mylestunglee/articulation70/images/kicad_left.png

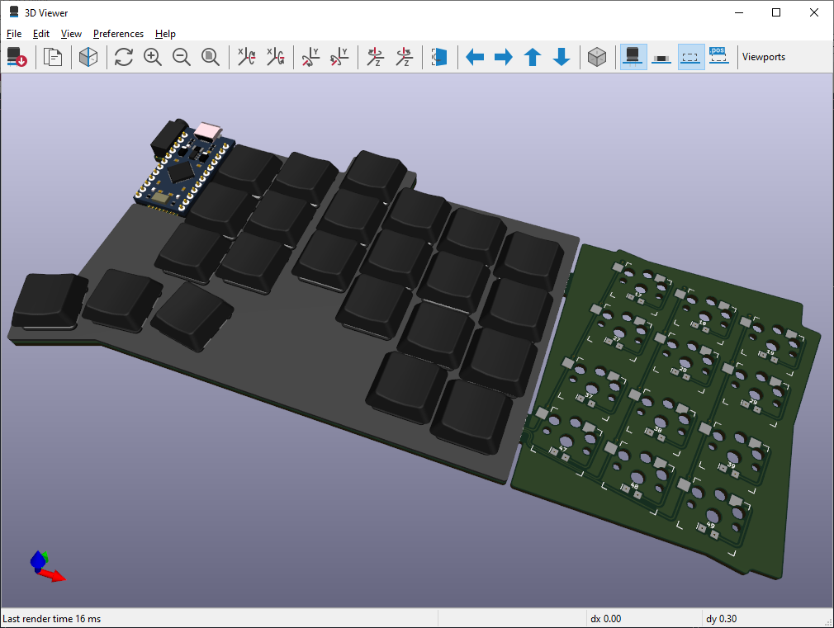
images/kicad_left.png
