mylestunglee/articulation70/images/kicad_plugin1_frames/04.png

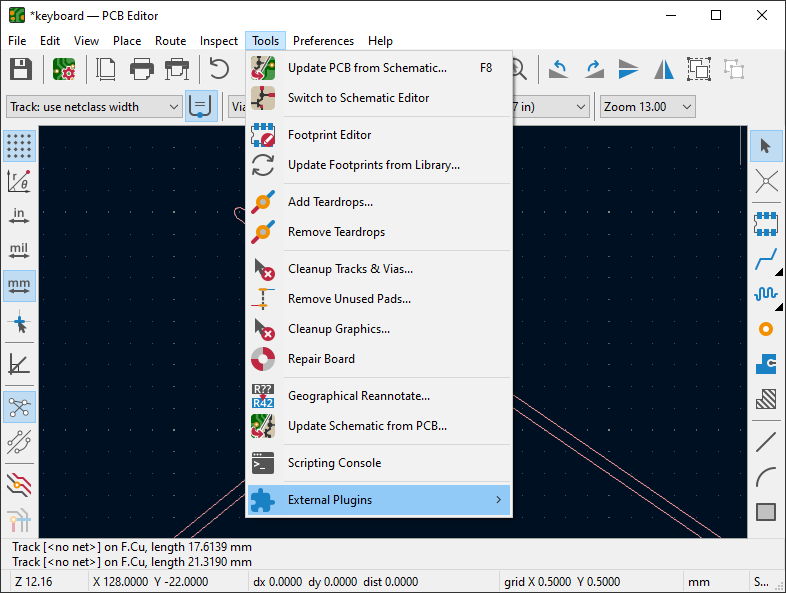
images/kicad_plugin1_frames/04.png
