mylestunglee/articulation70/images/kicad_plugin1_frames/07.png

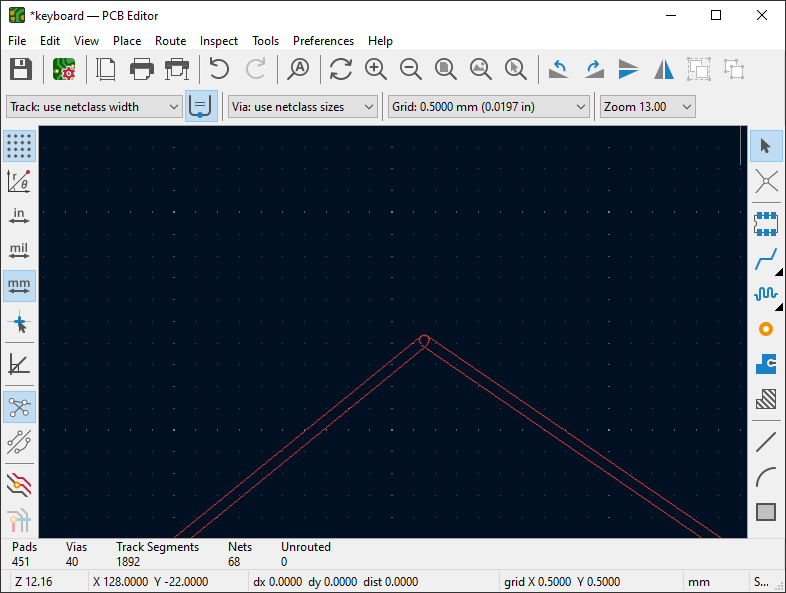
images/kicad_plugin1_frames/07.png
