mylestunglee/articulation70/images/kicad_plugin1_frames/09.png

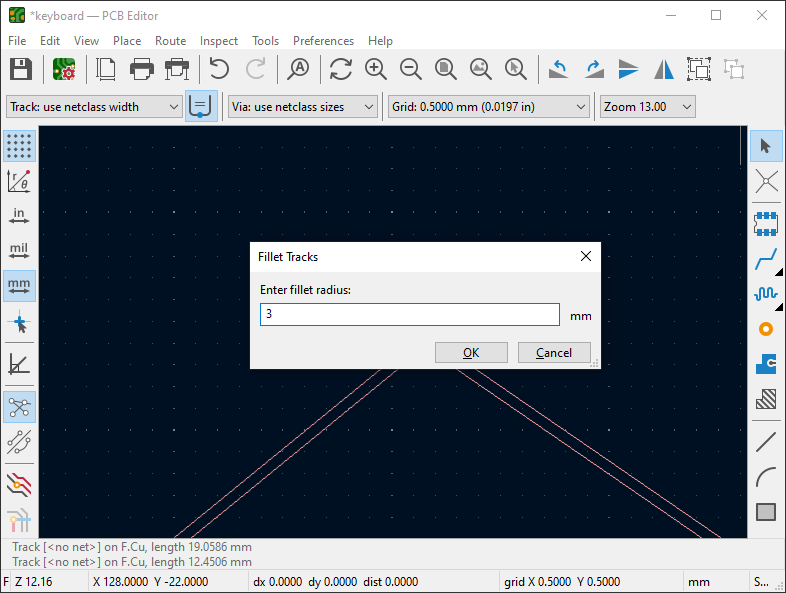
images/kicad_plugin1_frames/09.png
