mylestunglee/articulation70/images/photos/image1.jpeg

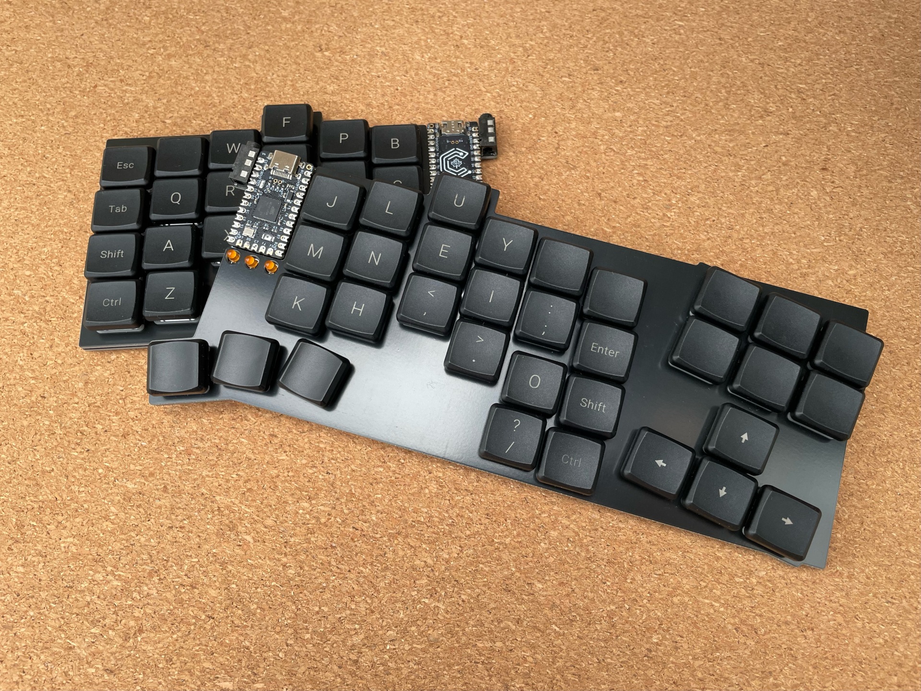
images/photos/image1.jpeg
