mylestunglee/articulation70/images/photos/image2.jpeg

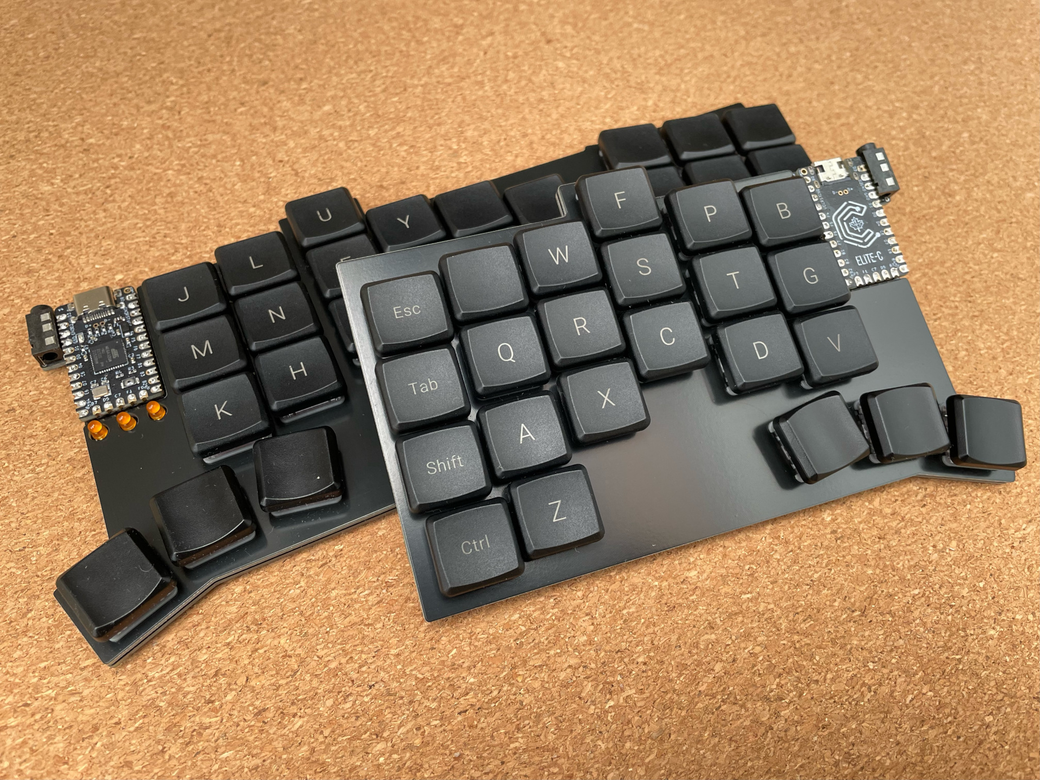
images/photos/image2.jpeg
