mylestunglee/articulation70/images/photos/image3.jpeg

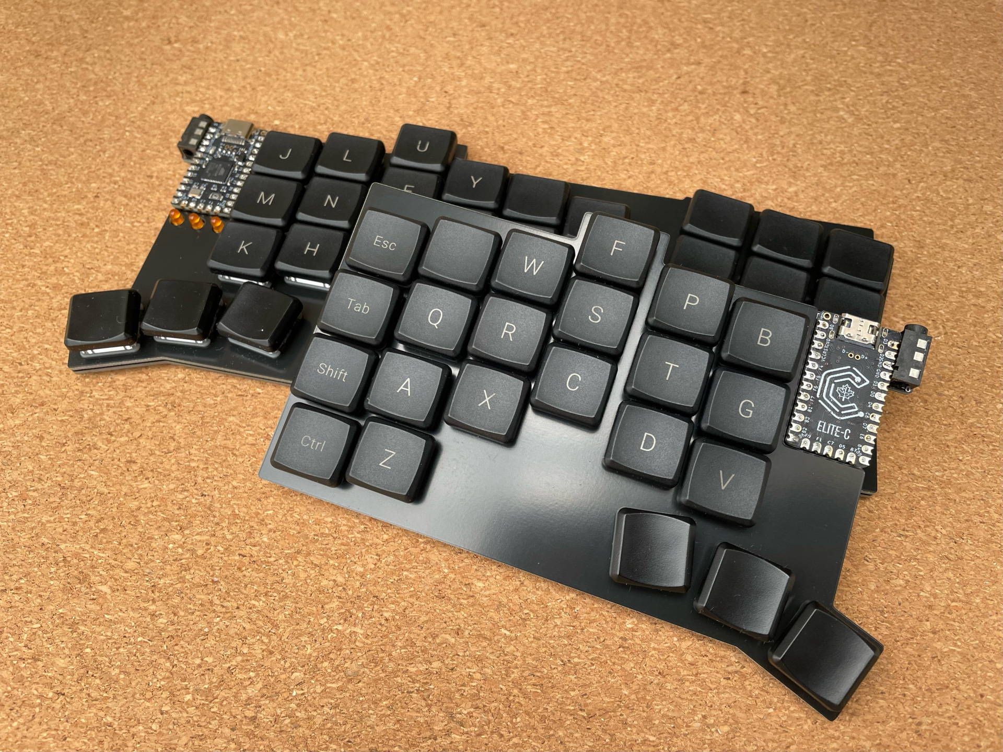
images/photos/image3.jpeg
