mylestunglee/articulation70/images/photos/image4.jpeg

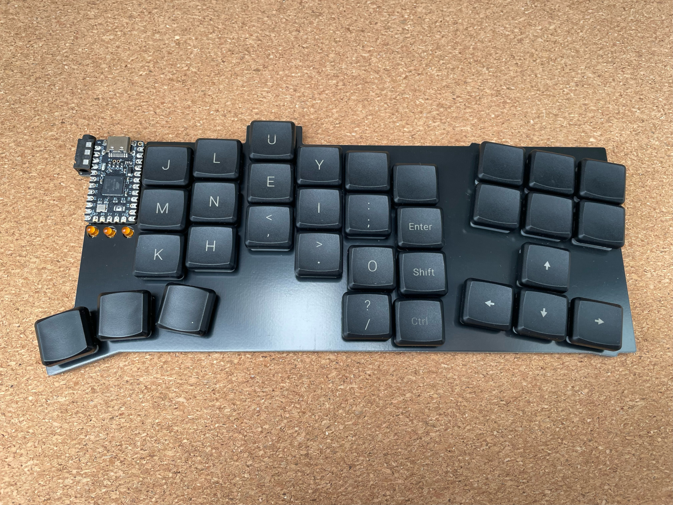
images/photos/image4.jpeg
