mylestunglee/articulation70/images/photos/image5.jpeg

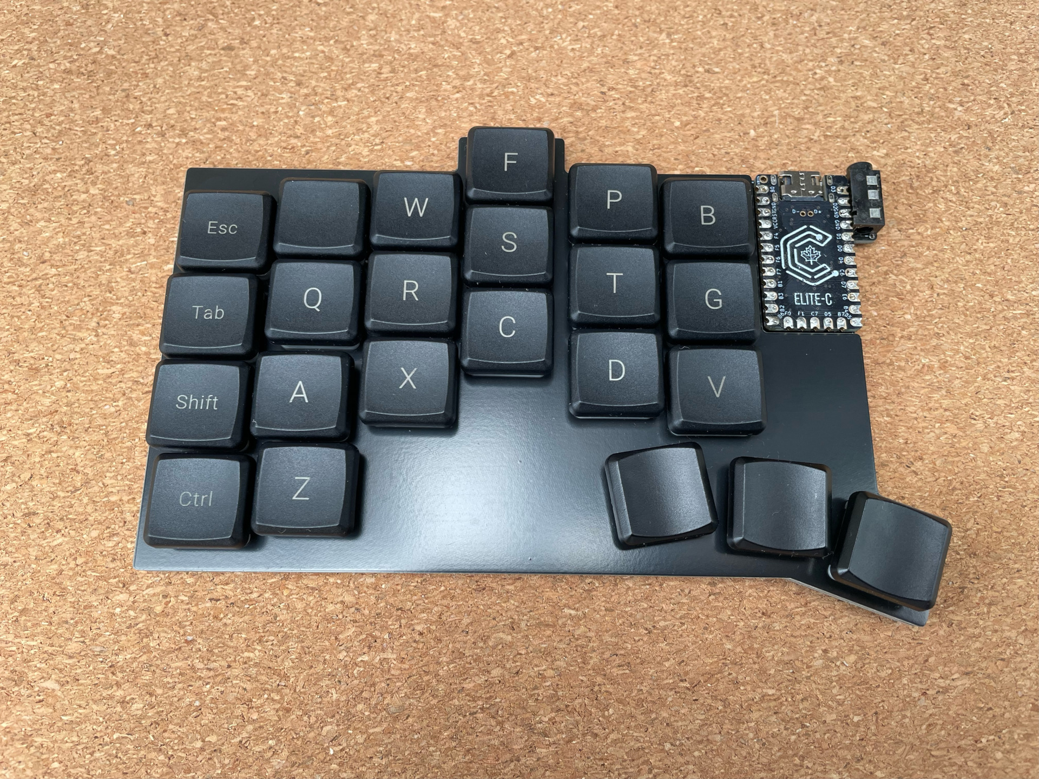
images/photos/image5.jpeg
