mylestunglee/articulation70/images/photos/pcb.jpeg

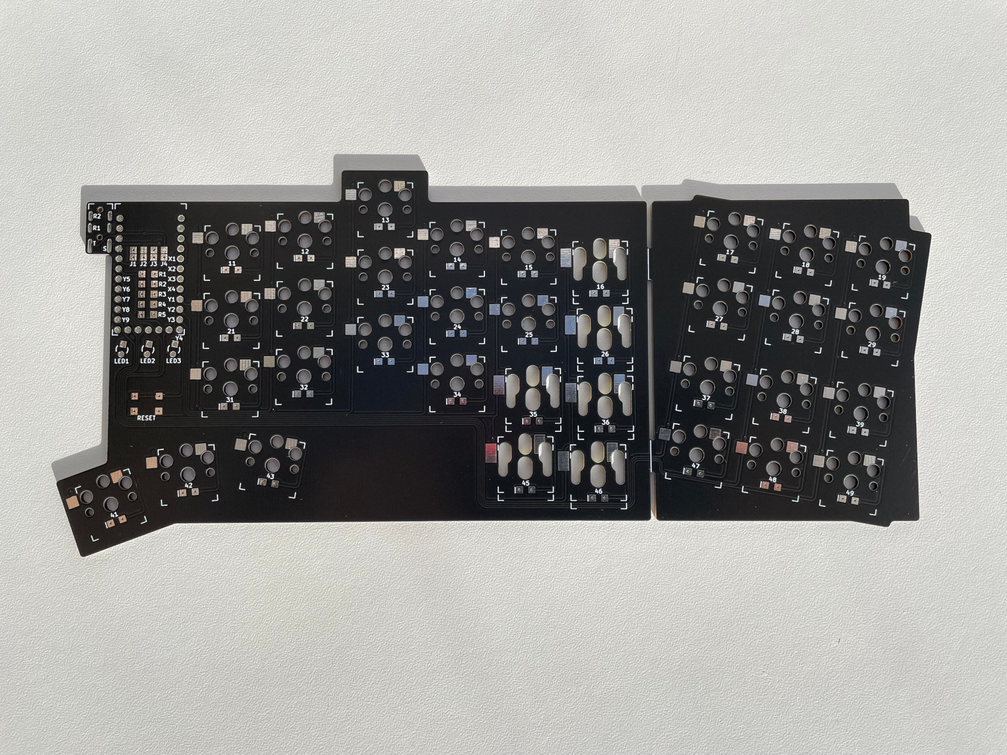
images/photos/pcb.jpeg
