mylestunglee/articulation70/images/photos_16x10/left.jpg

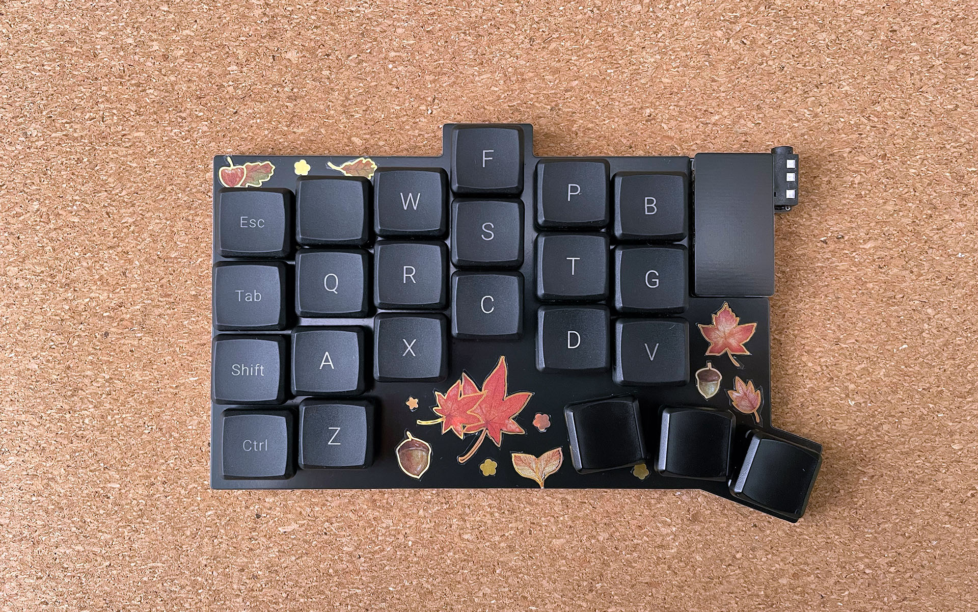
images/photos_16x10/left.jpg
